LibreSolar/mppt-2420-hc/build/mppt-2420-hc_schematic.pdf

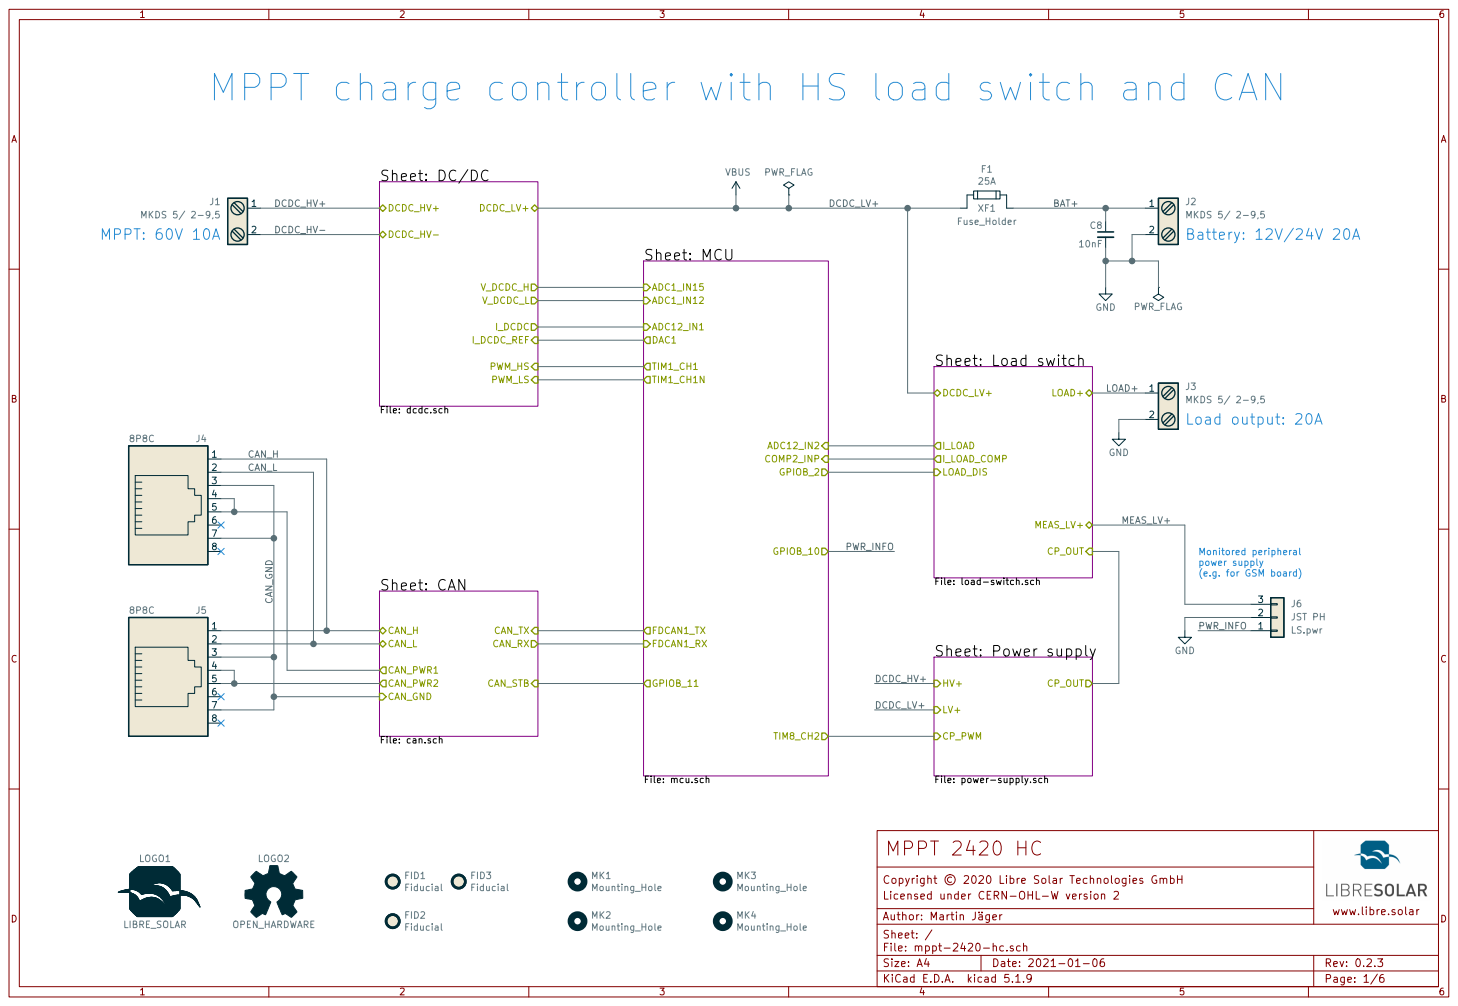
[picture p2: page 1]

File: load-switch.sch

LS.pwr FID1 Fiducial FID2 Fiducial

File: power-supply.sch

File: mppt-2420-hc.sch Sheet: / Copyright © 2020 Libre Solar Technologies GmbH

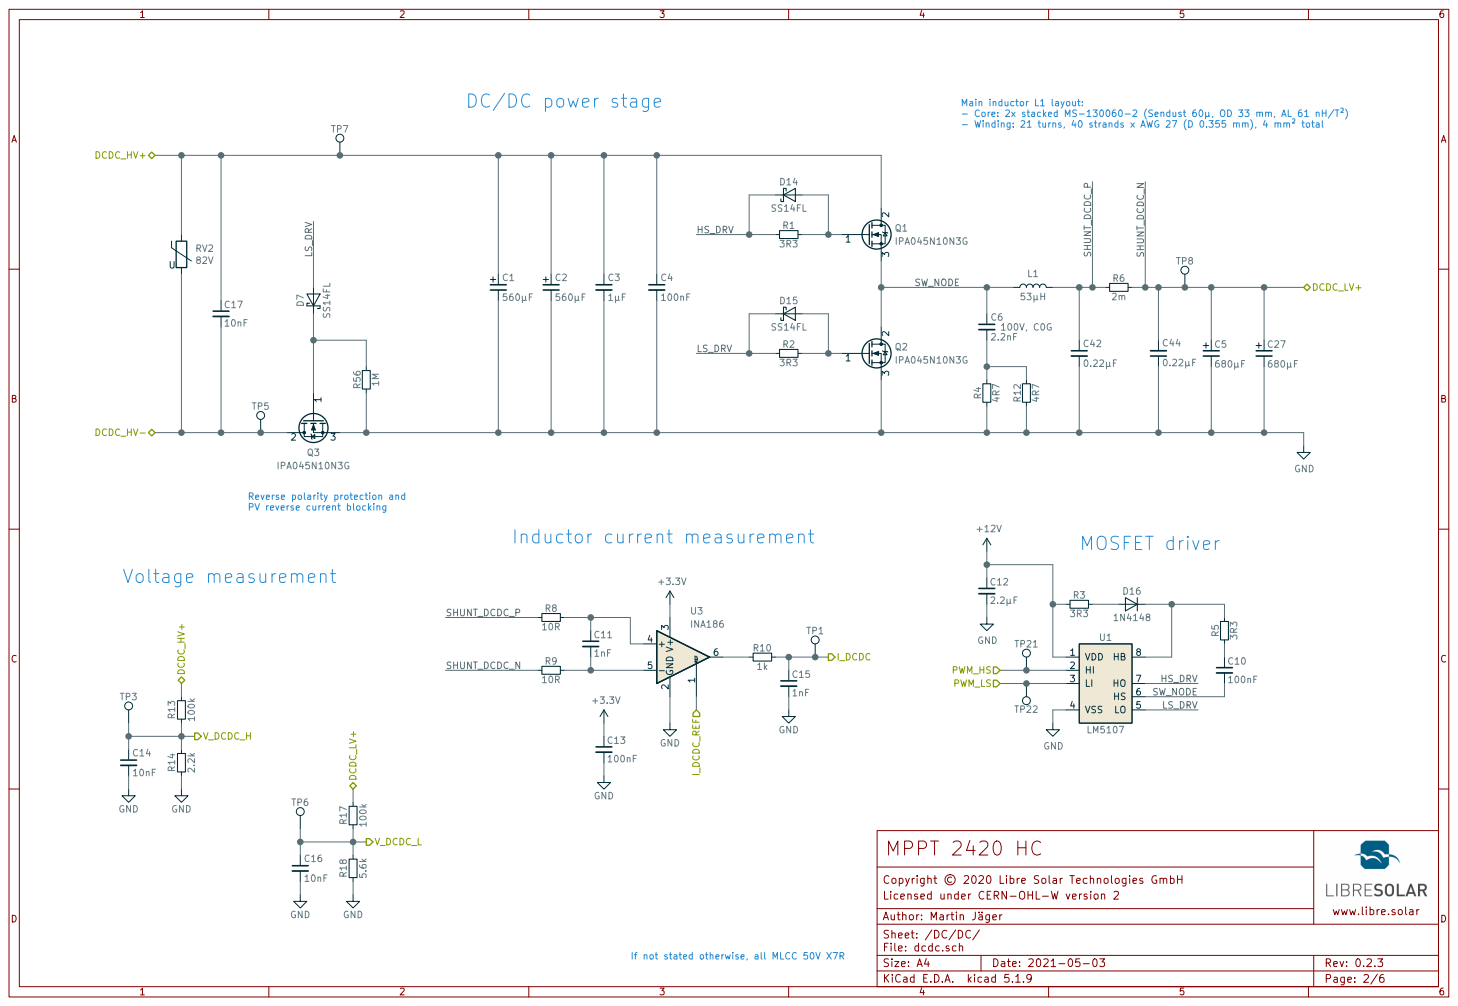
[picture p3: page 2]

DC/DC power stage

- Core: 2x stacked MS-130060-2 (Sendust 60µ, OD 33 mm, AL 61 nH/T²)
- Winding: 21 turns, 40 strands x AWG 27 (D 0.355 mm), 4 mm² total

Reverse polarity protection and
PV reverse current blocking

File: dcdc.sch Sheet: /DC/DC/ Copyright © 2020 Libre Solar Technologies GmbH

If not stated otherwise, all MLCC 50V X7R

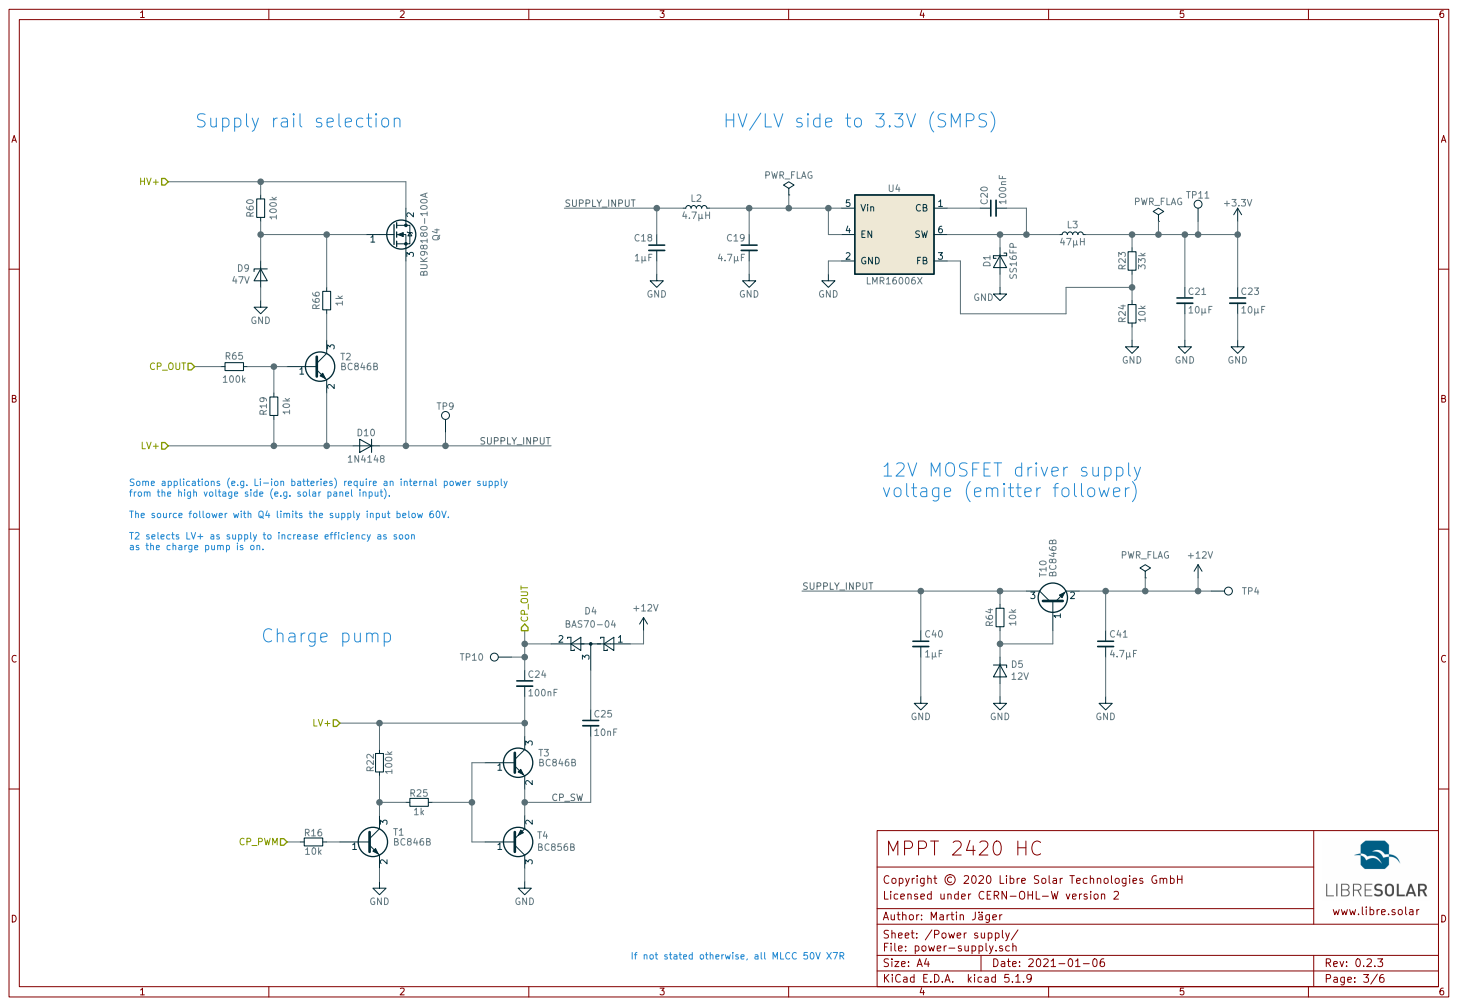
[picture p4: page 3]

HV/LV side to 3.3V (SMPS)

Some applications (e.g. Li-ion batteries) require an internal power supply
from the high voltage side (e.g. solar panel input).

The source follower with Q4 limits the supply input below 60V.

T2 selects LV+ as supply to increase efficiency as soon
as the charge pump is on.

If not stated otherwise, all MLCC 50V X7R Charge pump

Copyright © 2020 Libre Solar Technologies GmbH

Sheet: /Power supply/
File: power-supply.sch

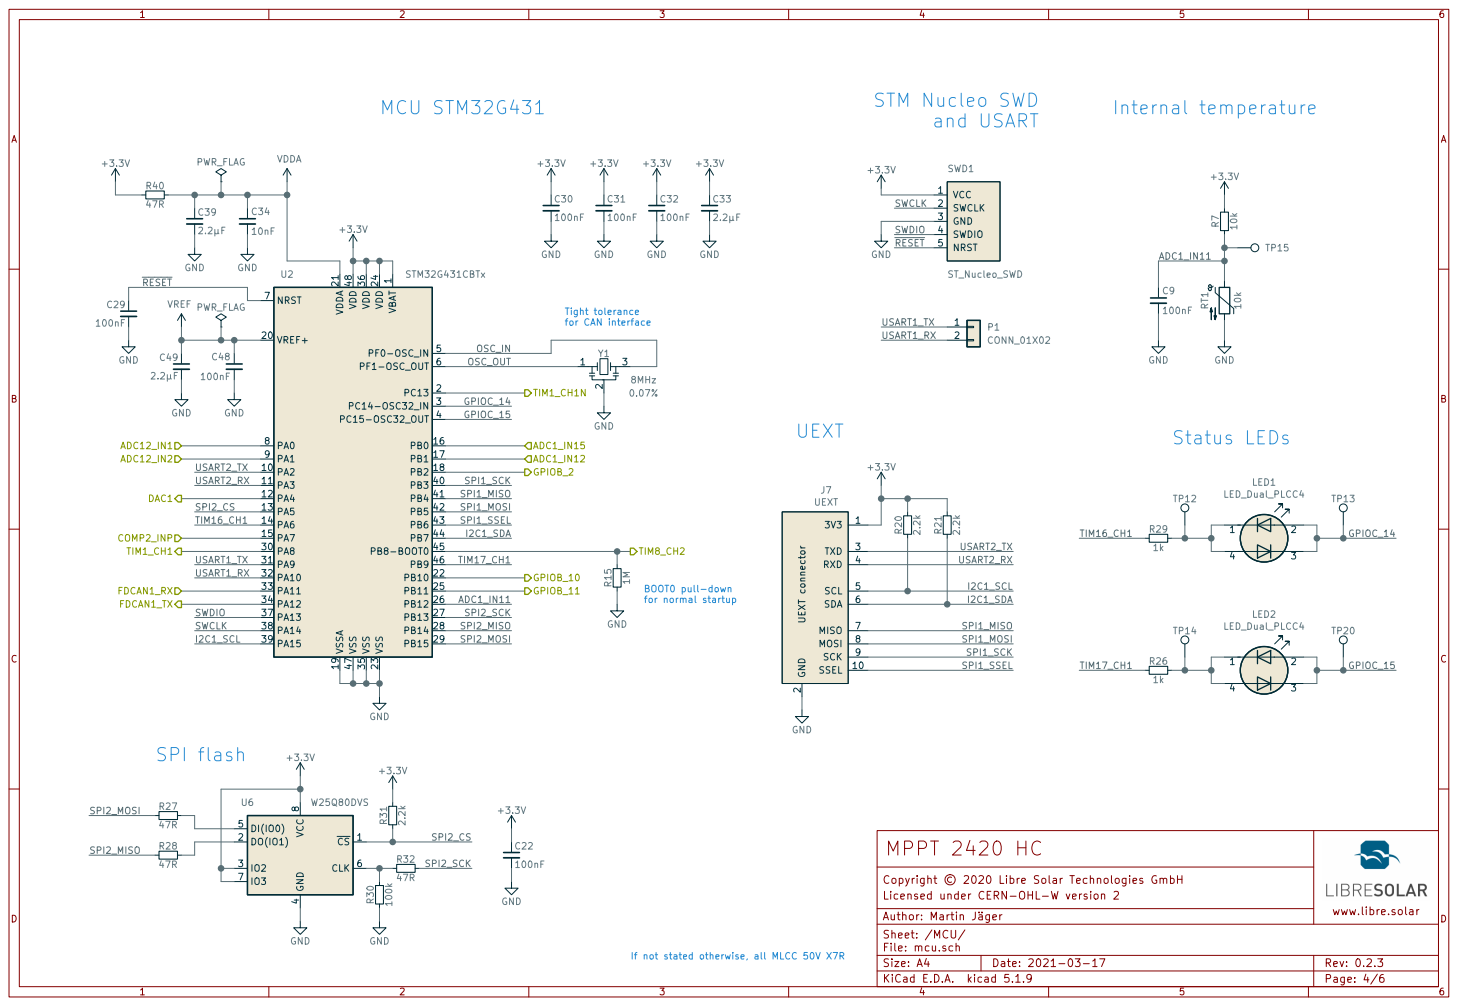
[picture p5: page 4]

If not stated otherwise, all MLCC 50V X7RUEXT

1 PA2 10 PA3 11 PA4 12 PA5 13 PA6 14 PA7 15 PB0 16 PB1 17 PB2 18 VSSA 19 PC13 2 VREF+ 20 VDDA 21 PB10 22 VSS 23 VDD 24 PB11 25 PB12 26 PB13 27 PB14 28 PB15 29 PC14-OSC32_IN 3 PA8 30 PA9 31 PA10 32 PA11 33 PA12 34 VSS 35 VDD 36 PA13 37 PA14 38 PA15 39 PC15-OSC32_OUT 4 PB3 40 PB4 41 PB5 42 PB6 43 PB7 44 PB8-BOOT0 45 PB9 46 VSS 47 VDD 48 PF0-OSC_IN 5 PF1-OSC_OUT 6 NRST 7 PA0 8 PA1 9 U2 STM32G431CBTx C39

for CAN interface SPI flash

2 TXD 3 SCL 5 SDA 6 MISO 7 MOSI 8 SCK 9

File: mcu.sch Sheet: /MCU/ Copyright © 2020 Libre Solar Technologies GmbH

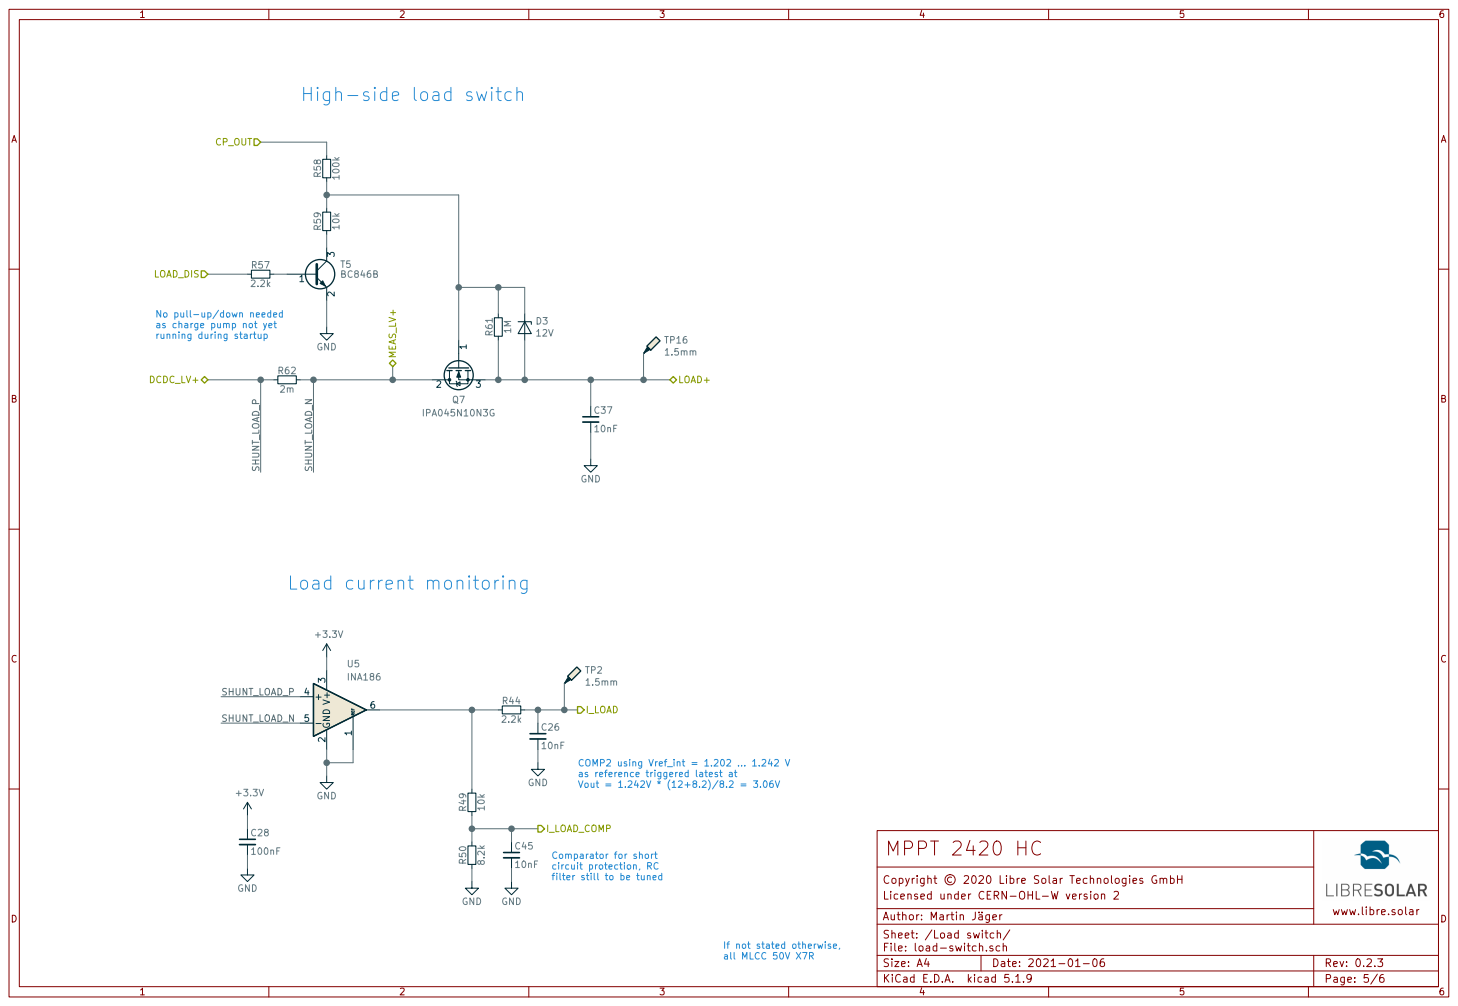
[picture p6: page 5]

No pull-up/down needed
as charge pump not yet
running during startup

COMP2 using Vref_int = 1.202 ... 1.242 V
as reference triggered latest at
Vout = 1.242V * (12+8.2)/8.2 = 3.06V

Comparator for short
circuit protection, RC
filter still to be tuned

File: load-switch.sch Sheet: /Load switch/ Copyright © 2020 Libre Solar Technologies GmbH

www.libre.solar

Licensed under CERN-OHL-W version 2 Author: Martin Jäger

If not stated otherwise, all MLCC 50V X7R

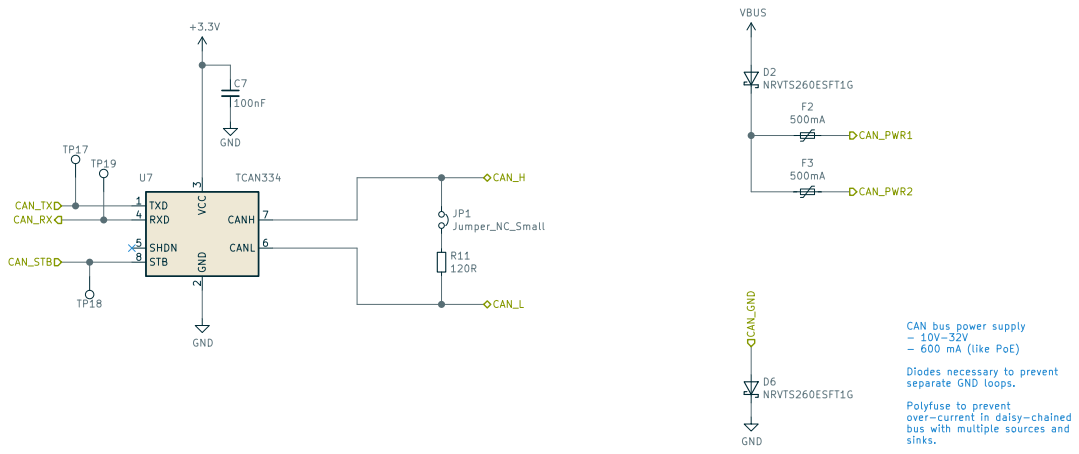
[picture p7: page 6]

3 RXD 4 SHDN 5 CANL 6 CANH 7 STB 8U7 TCAN334 R11

Diodes necessary to prevent
separate GND loops.

Polyfuse to prevent
over-current in daisy-chained
bus with multiple sources and sinks.

File: can.sch Sheet: /CAN/ Copyright © 2020 Libre Solar Technologies GmbH

www.libre.solar

Licensed under CERN-OHL-W version 2 Author: Martin Jäger
